me72rafal/kff-experimental/firmware/cartridges/cartridge.c

/*
 * Copyright (c) 2019-2025 Kim Jørgensen
 *
 * This software is provided 'as-is', without any express or implied
 * warranty.  In no event will the authors be held liable for any damages
 * arising from the use of this software.
 *
 * Permission is granted to anyone to use this software for any purpose,
 * including commercial applications, and to alter it and redistribute it
 * freely, subject to the following restrictions:
 *
 * 1. The origin of this software must not be misrepresented; you must not
 *    claim that you wrote the original software. If you use this software
 *    in a product, an acknowledgment in the product documentation would be
 *    appreciated but is not required.
 * 2. Altered source versions must be plainly marked as such, and must not be
 *    misrepresented as being the original software.
 * 3. This notice may not be removed or altered from any source distribution.
 */

#include "cartridge.h"

// Current ROM or RAM bank pointer
static u8 *crt_ptr;

// Current ROM bank pointer (only used by some cartridges)
static u8 *crt_rom_ptr;

static u32 special_button;
static u32 freezer_state;


// C64 bus timing
static u32 phi2_hiram;
//static u32 phi2_adr_stable;
static u32 phi2_cpu_start;
static u32 phi2_write_delay;
static u32 phi2_cpu_end;
static u32 phi2_vic_start;
static u32 phi2_vic_delay;
static u32 phi2_vic_end;

// Ordered by cartridge id
#include "crt_normal.c"
#include "action_replay_4x.c"
#include "kcs_power_cartridge.c"
#include "final_cartridge_3.c"
#include "simons_basic.c"
#include "super_games.c"
#include "epyx_fastload.c"
#include "c64gs_system_3.c"
#include "warpspeed.c"
#include "dinamic.c"
#include "zaxxon.c"
#include "magic_desk.c"
#include "super_snapshot_5.c"
#include "comal80.c"
#include "ross.c"
#include "easyflash.c"
#include "easyflash_3.c"
#include "prophet64.c"
#include "freeze_machine.c"
#include "pagefox.c"
#include "rgcd.c"
#include "c128_normal.c"
#include "kff.c"
#include "destest_switch.c"
#include "kernal.c"

#define NTSC_OR_PAL_HANDLER(name)     name##_handler

static void (*crt_get_handler(u32 cartridge_type, bool vic_support)) (void)
{
    switch (cartridge_type)
    {
        case CRT_NORMAL_CARTRIDGE:
            return NTSC_OR_PAL_HANDLER(crt);

// Make room for debug logging by disabling support for some cartridges
#if !(LOG_ENABLED)
        case CRT_ACTION_REPLAY:
            return NTSC_OR_PAL_HANDLER(ar4x);

        case CRT_KCS_POWER_CARTRIDGE:
            return NTSC_OR_PAL_HANDLER(kcs);

        case CRT_FINAL_CARTRIDGE_III:
            return NTSC_OR_PAL_HANDLER(fc3);

        case CRT_SIMONS_BASIC:
            return simons_basic_handler;

        case CRT_SUPER_GAMES:
            return super_games_handler;

        case CRT_EPYX_FASTLOAD:
            return epyx_handler;

        case CRT_C64_GAME_SYSTEM_SYSTEM_3:
            return c64gs_handler;

        case CRT_WARP_SPEED:
        case CRT_MACH_5:
        case CRT_C128_WARP_SPEED:
            return NTSC_OR_PAL_HANDLER(warpspeed);

        case CRT_DINAMIC:
            return dinamic_handler;

        case CRT_ZAXXON_SUPER_ZAXXON:
            return zaxxon_handler;

        case CRT_FUN_PLAY_POWER_PLAY:
        case CRT_MAGIC_DESK_DOMARK_HES_AUSTRALIA:
            return magic_desk_handler;

        case CRT_SUPER_SNAPSHOT_V5:
            return NTSC_OR_PAL_HANDLER(ss5);

        case CRT_COMAL_80:
            return comal80_handler;

        case CRT_KERNAL:
            if ((dat_file.flags & DAT_FLAG_PLA) == 0) {
                return kernalo_handler;
            } else {
                return kernalf_handler;
            }

        case CRT_ROSS:
            return ross_handler;
#endif
        case CRT_OCEAN_TYPE_1:
        case CRT_EASYFLASH:
            if (cartridge_type != CRT_EASYFLASH || vic_support)
            {
                return NTSC_OR_PAL_HANDLER(ef);
            }
            return ef3_handler;

        case CRT_PROPHET64:
        case CRT_DREAN:
            return prophet64_handler;

        case CRT_FREEZE_FRAME:
        case CRT_FREEZE_MACHINE:
            return NTSC_OR_PAL_HANDLER(fm);

        case CRT_PAGEFOX:
            return pagefox_handler;

        case CRT_RGCD:
            return rgcd_handler;

        case CRT_C128_NORMAL_CARTRIDGE:
            return NTSC_OR_PAL_HANDLER(c128);
            
        case CRT_DESTEST_SWITCH:
            return NTSC_OR_PAL_HANDLER(dts);
    }

    return NULL;
}

static void crt_init(DAT_CRT_HEADER *crt_header)
{
    bool ntsc = c64_is_ntsc();
    if (!ntsc) {
        phi2_hiram = 83;                                           // for CRT_KERNAL
        //phi2_adr_stable = 152;                                      // for by CRT_MAGIC_FORMEL
        phi2_cpu_start = PAL_PHI2_CPU_START;
        phi2_write_delay = PAL_PHI2_WRITE_DELAY;
        phi2_cpu_end = PAL_PHI2_CPU_END-1;
        phi2_vic_start = PAL_PHI2_VIC_START;
        phi2_vic_delay = PAL_PHI2_VIC_DELAY;
        phi2_vic_end = PAL_PHI2_VIC_END;
    }
    else {
        phi2_hiram = 80;                                             // for CRT_KERNAL
        //phi2_adr_stable = 146;                                        // for CRT_MAGIC_FORMEL
        phi2_cpu_start = NTSC_PHI2_CPU_START;
        phi2_write_delay = NTSC_PHI2_WRITE_DELAY;
        phi2_cpu_end = NTSC_PHI2_CPU_END;
        phi2_vic_start = NTSC_PHI2_VIC_START;
        phi2_vic_delay = NTSC_PHI2_VIC_DELAY;
        phi2_vic_end = NTSC_PHI2_VIC_END;
    }
    switch (crt_header->type)
    {
        case CRT_ACTION_REPLAY:
            ar4x_init();
            break;

        case CRT_KCS_POWER_CARTRIDGE:
            kcs_init();
            break;

        case CRT_FINAL_CARTRIDGE_III:
            fc3_init();
            break;

        case CRT_EPYX_FASTLOAD:
            epyx_init();
            break;

        case CRT_WARP_SPEED:
        case CRT_MACH_5:
        case CRT_C128_WARP_SPEED:
            warpspeed_init(crt_header);
            break;

        case CRT_ZAXXON_SUPER_ZAXXON:
            zaxxon_init();
            break;

        case CRT_FUN_PLAY_POWER_PLAY:
        case CRT_MAGIC_DESK_DOMARK_HES_AUSTRALIA:
            magic_desk_init();
            break;

        case CRT_SUPER_SNAPSHOT_V5:
            ss5_init();
            break;

        case CRT_COMAL_80:
            comal80_init();
            break;
        
        case CRT_KERNAL:
            kernal_init();
            break;

        case CRT_ROSS:
            ross_init(crt_header);
            break;

        case CRT_EASYFLASH:
            ef_init();
            break;

        case CRT_FREEZE_FRAME:
        case CRT_FREEZE_MACHINE:
            fm_init(crt_header);
            break;

        case CRT_PAGEFOX:
            pagefox_init();
            break;

        case CRT_RGCD:
            rgcd_init(crt_header);
            break;
        
        case CRT_DESTEST_SWITCH:
            dts_init();
            break;
    }
}

static void crt_install_handler(DAT_CRT_HEADER *crt_header)
{
    u32 state = STATUS_LED_ON;
    if (!(crt_header->type & CRT_C128_CARTRIDGE))
    {
        if (crt_header->exrom)
        {
            state |= C64_EXROM_HIGH;
        }
        else
        {
            state |= C64_EXROM_LOW;
        }

        if (crt_header->game)
        {
            state |= C64_GAME_HIGH;
        }
        else
        {
            state |= C64_GAME_LOW;
        }
    }
    else
    {
        state |= CRT_PORT_NONE;
    }

    C64_CRT_CONTROL(state);

    crt_ptr = crt_banks[0];
    crt_init(crt_header);

    u32 cartridge_type = crt_header->type;
    bool vic_support = (crt_header->flags & CRT_FLAG_VIC) != 0;
    void (*handler)(void) = crt_get_handler(cartridge_type, vic_support);
    C64_INSTALL_HANDLER(handler);
}

static bool crt_is_supported(u32 cartridge_type)
{
    return crt_get_handler(cartridge_type, false) != NULL;
}
