me72rafal/kff-experimental/firmware/file_types.h

/*
 * Copyright (c) 2019-2023 Kim Jørgensen
 *
 * This software is provided 'as-is', without any express or implied
 * warranty.  In no event will the authors be held liable for any damages
 * arising from the use of this software.
 *
 * Permission is granted to anyone to use this software for any purpose,
 * including commercial applications, and to alter it and redistribute it
 * freely, subject to the following restrictions:
 *
 * 1. The origin of this software must not be misrepresented; you must not
 *    claim that you wrote the original software. If you use this software
 *    in a product, an acknowledgment in the product documentation would be
 *    appreciated but is not required.
 * 2. Altered source versions must be plainly marked as such, and must not be
 *    misrepresented as being the original software.
 * 3. This notice may not be removed or altered from any source distribution.
 */

// From https://vice-emu.sourceforge.io/vice_17.html
typedef enum
{
    CRT_NORMAL_CARTRIDGE = 0x00,
    CRT_ACTION_REPLAY,
    CRT_KCS_POWER_CARTRIDGE,
    CRT_FINAL_CARTRIDGE_III,
    CRT_SIMONS_BASIC,
    CRT_OCEAN_TYPE_1,
    CRT_EXPERT_CARTRIDGE,
    CRT_FUN_PLAY_POWER_PLAY,
    CRT_SUPER_GAMES,
    CRT_ATOMIC_POWER,
    CRT_EPYX_FASTLOAD,
    CRT_WESTERMANN_LEARNING,
    CRT_REX_UTILITY,
    CRT_FINAL_CARTRIDGE_I,
    CRT_C64_GAME_SYSTEM_SYSTEM_3,
    CRT_WARP_SPEED,
    CRT_DINAMIC,
    CRT_ZAXXON_SUPER_ZAXXON,
    CRT_MAGIC_DESK_DOMARK_HES_AUSTRALIA,
    CRT_SUPER_SNAPSHOT_V5,
    CRT_COMAL_80,
    CRT_STRUCTURED_BASIC,
    CRT_ROSS,
    CRT_DELA_EP64,
    CRT_DELA_EP7X8,
    CRT_DELA_EP256,
    CRT_REX_EP256,
    CRT_MIKRO_ASSEMBLER,
    CRT_FINAL_CARTRIDGE_PLUS,
    CRT_ACTION_REPLAY_4,
    CRT_STARDOS,
    CRT_EASYFLASH,
    CRT_EASYFLASH_XBANK,
    CRT_CAPTURE,
    CRT_ACTION_REPLAY_3,
    CRT_RETRO_REPLAY,
    CRT_MMC64,
    CRT_MMC_REPLAY,
    CRT_IDE64,
    CRT_SUPER_SNAPSHOT_V4,
    CRT_IEEE_488,
    CRT_GAME_KILLER,
    CRT_PROPHET64,
    CRT_EXOS,
    CRT_FREEZE_FRAME,
    CRT_FREEZE_MACHINE,
    CRT_SNAPSHOT64,
    CRT_SUPER_EXPLODE_V5_0,
    CRT_MAGIC_VOICE,
    CRT_ACTION_REPLAY_2,
    CRT_MACH_5,
    CRT_DIASHOW_MAKER,
    CRT_PAGEFOX,
    CRT_KINGSOFT,
    CRT_SILVERROCK_128K_CARTRIDGE,
    CRT_FORMEL_64,
    CRT_RGCD,
    CRT_RR_NET_MK3,
    CRT_EASYCALC,
    CRT_GMOD2,
    CRT_MAX_BASIC,
    CRT_GMOD3,
    CRT_ZIPP_CODE_48,
    CRT_BLACKBOX_V8,
    CRT_BLACKBOX_V3,
    CRT_BLACKBOX_V4,
    CRT_REX_RAM_FLOPPY,
    CRT_BIS_PLUS,
    CRT_SD_BOX,
    CRT_MULTIMAX,
    CRT_BLACKBOX_V9,
    CRT_LT_KERNAL_HOST_ADAPTOR,
    CRT_RAMLINK,
    CRT_DREAN,
    CRT_IEEE_FLASH_64,
    CRT_TURTLE_GRAPHICS_II,
	CRT_FREEZE_FRAME_MK2,

    // KFF specific extensions
    CRT_DESTEST_SWITCH = 0x6000,
    CRT_KERNAL = 0x7000,
    
    CRT_C128_CARTRIDGE = 0x8000,
    CRT_C128_NORMAL_CARTRIDGE = CRT_C128_CARTRIDGE,
    CRT_C128_WARP_SPEED
} CRT_TYPE;

typedef enum
{
    CRT_CHIP_ROM = 0x00,
    CRT_CHIP_RAM,
    CRT_CHIP_FLASH
} CRT_CHIP_TYPE;

#pragma pack(push)
#pragma pack(1)
typedef struct
{
    u8 signature[16];
    u32 header_length;
    u16 version;
    u16 cartridge_type;
    u8 exrom;
    u8 game;
    u8 hardware_revision;
    u8 reserved[5];
    u8 cartridge_name[32];
} CRT_HEADER;

typedef struct
{
    u8 signature[4];
    u32 packet_length;
    u16 chip_type;
    u16 bank;
    u16 start_address;
    u16 image_size;
} CRT_CHIP_HEADER;

typedef struct
{
    char signature[8];
    char filename[17];
    u8 rel_record_size;
} P00_HEADER;
#pragma pack(pop)

typedef enum
{
    FILE_DIR        = 0x00,
    FILE_DIR_UP,
    FILE_CRT,
    FILE_PRG,
    FILE_P00,
    FILE_D64,
    FILE_D64_STAR,
    FILE_D64_PRG,
    FILE_T64,
    FILE_T64_PRG,
    FILE_ROM,
    FILE_TXT,

    FILE_UPD        = 0xfd,
    FILE_DAT,
    FILE_UNKNOWN
} FILE_TYPE;

typedef enum
{
    DAT_FLAG_PERSIST_BASIC      = 0x0001,
  	DAT_FLAG_AUTOSTART_PRG      = 0x0008,
    DAT_FLAG_AUTOSTART_D64      = 0x0010,
    DAT_FLAG_DEVICE_NUM_D64_1   = 0x0020,
    DAT_FLAG_DEVICE_NUM_D64_2   = 0x0040,
    DAT_FLAG_DEVICE_NUM_D64_3   = 0x0080,
    DAT_FLAG_PLA                = 0x0100
} DAT_FLAGS;

#define DAT_FLAG_DEVICE_D64_POS 0x02
#define DAT_FLAG_DEVICE_D64_MSK (0x07 << DAT_FLAG_DEVICE_D64_POS)

typedef enum
{
    DAT_NONE = 0x00,
    DAT_CRT,
    DAT_PRG,
    DAT_USB,
    DAT_DISK,
    DAT_TXT,
    DAT_BASIC,
    DAT_KILL,
    DAT_KILL_C128,
    DAT_DIAG
} DAT_BOOT_TYPE;

typedef enum
{
    CRT_FLAG_NONE       = 0x00,
    CRT_FLAG_UPDATED    = 0x01, // EasyFlash CRT has been updated via EAPI

    CRT_FLAG_VIC        = 0x80  // Support VIC/C128 2MHz mode reads (EF only)
} DAT_CRT_FLAGS;

typedef enum
{
    DISK_MODE_FS    = 0x00, // Use filesystem
    DISK_MODE_D64   = 0x01  // Use D64 disk image
} DAT_DISK_MODE;

#pragma pack(push)
#pragma pack(1)
typedef struct
{
    u16 type;           // CRT_TYPE
    u8 hw_rev;          // Cartridge hardware revision
    u8 exrom;           // EXROM line status
    u8 game;            // GAME line status
    u8 banks;           // Number of 16k CRT banks in use (0-64)
    u8 flags;           // DAT_CRT_FLAGS
    u32 flash_hash;     // Used id crt_banks > 4
} DAT_CRT_HEADER;

typedef struct
{
    u16 size;
    u16 element;        // Used if file is a T64 or D64
    char name[17];      // Used if file is a P00, T64, or D64
} DAT_PRG_HEADER;

typedef struct
{
    u8 mode;            // DAT_DISK_MODE
} DAT_DISK_HEADER;

typedef struct
{
    u8 signature[8];    // DAT_SIGNATURE

    u16 flags;           // DAT_FLAGS
    u8 boot_type;       // DAT_BOOT_TYPE
    s8 phi2_offset;

    union
    {
        DAT_CRT_HEADER crt;     // boot_type == DAT_CRT
        DAT_PRG_HEADER prg;     // boot_type == DAT_PRG
        DAT_DISK_HEADER disk;   // boot_type == DAT_DISK
    };

    char path[512];
    char file[128];
} DAT_HEADER;
#pragma pack(pop)

#define ELEMENT_NOT_SELECTED 0xffff
#define DAT_SIGNATURE "KungFu:\1"

static DAT_HEADER dat_file;
